woshishuaige2/awesome-dodeca-pen/Code/Kalman/imu_plots_v2.png

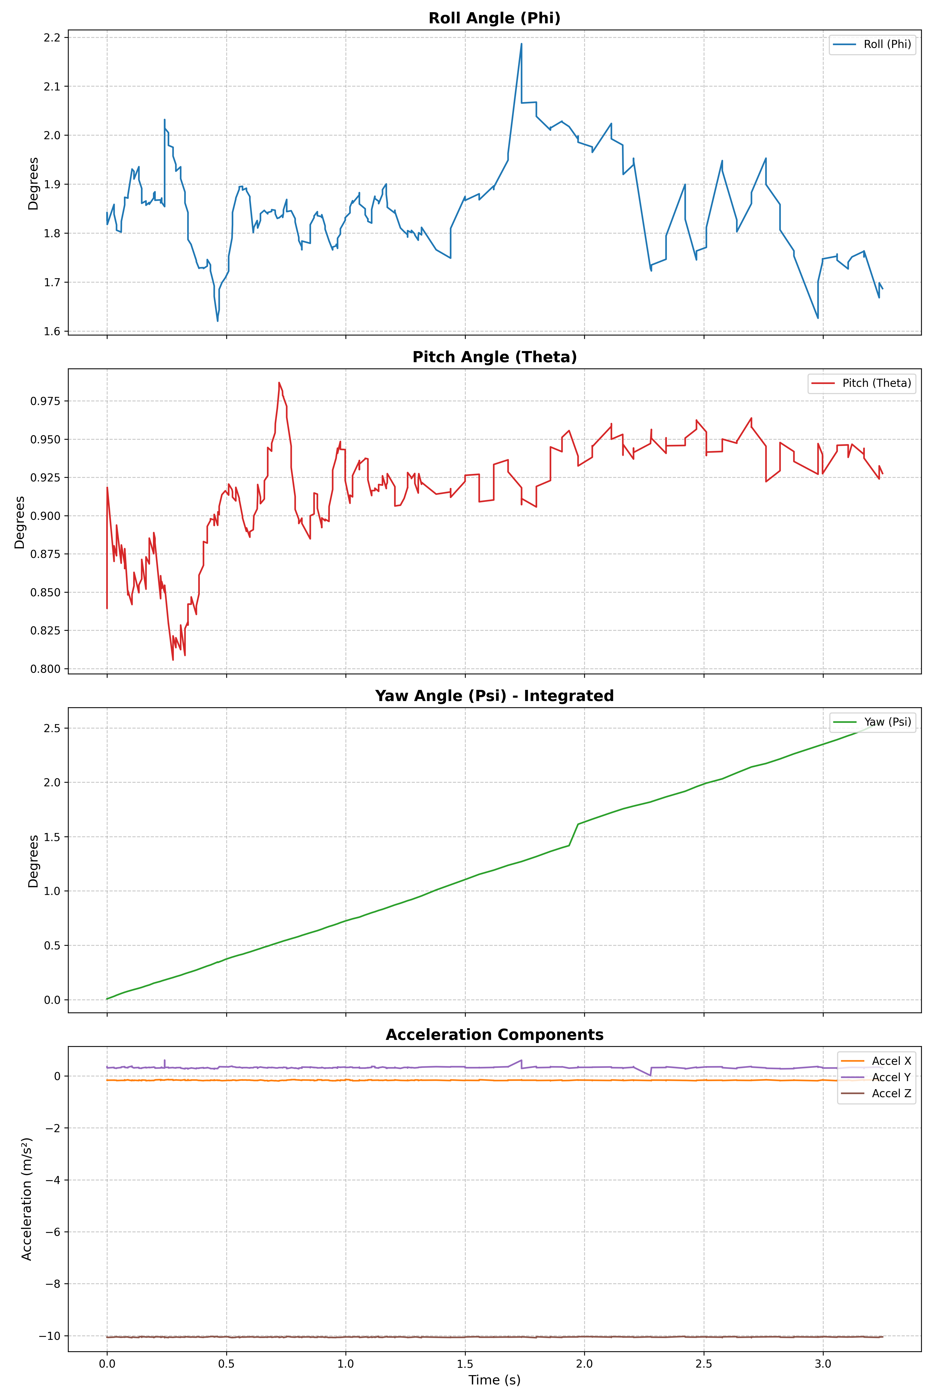
Code/Kalman/imu_plots_v2.png
